daguilar43/proyectoEmbebidos/Riot/sd1306_i2c/main.c

/*
 * Copyright (C) 2016 Bas Stottelaar <basstottelaar@gmail.com>
 *
 * This file is subject to the terms and conditions of the GNU Lesser
 * General Public License v2.1. See the file LICENSE in the top level
 * directory for more details.
 */

/**
 * @ingroup     tests
 * @{
 *
 * @file
 * @brief       Test application for the U8g2 package.
 *
 * @author      Bas Stottelaar <basstottelaar@gmail.com>
 *
 * @}
 */

#ifndef INDEX_DRIVER_HW_I2C
#error "INDEX_DRIVER_HW_I2C not defined"
#endif

#ifndef TEST_ADDR
#error "TEST_ADDR not defined"
#endif

#ifndef SETUP_DISPLAY
#error "SETUP_DISPLAY not defined"
#endif

#ifndef TEST_PIN_RESET
#error "TEST_PIN_RESET not defined"
#endif

#include <stdio.h>

#include "periph/gpio.h"
#include "periph/i2c.h"

#include "timex.h"
#include "ztimer.h"

#include "u8g2.h"
#include "u8x8_riotos.h"

/**
 * @brief   RIOT-OS logo, 64x32 pixels at 8 pixels per byte.
 */
static const uint8_t logo[] = {

// 'amiplanta128x64', 128x64px
0xff, 0xff, 0xff, 0xff, 0xff, 0xff, 0xff, 0xff, 0xff, 0xff, 0xff, 0xff, 0xff, 0xff, 0xff, 0xff, 
0xff, 0xff, 0xff, 0xff, 0xff, 0xff, 0xff, 0xf8, 0x1f, 0xff, 0xff, 0xff, 0xff, 0xff, 0xff, 0xff, 
0xff, 0xff, 0xff, 0xff, 0xff, 0xff, 0xff, 0xe0, 0x07, 0xff, 0xff, 0xff, 0xff, 0xff, 0xff, 0xff, 
0xff, 0xff, 0xff, 0xff, 0xff, 0xff, 0xff, 0xc3, 0xe1, 0xff, 0xff, 0xff, 0xff, 0xff, 0xff, 0xff, 
0xff, 0xff, 0xff, 0xff, 0xff, 0xff, 0xff, 0x0f, 0xf0, 0xff, 0xff, 0xff, 0xff, 0xff, 0xff, 0xff, 
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

    u8g2_InitDisplay(&u8g2);
    u8g2_SetPowerSave(&u8g2, 0);

    /* start drawing in a loop */
    puts("Drawing on screen.");

    while (1) {
        u8g2_FirstPage(&u8g2);

        do {
            u8g2_SetDrawColor(&u8g2, 1);
            u8g2_SetFont(&u8g2, u8g2_font_helvB12_tf);

            switch (screen) {
                case 0:
                    u8g2_DrawStr(&u8g2, 12, 22, "THIS");
                    break;
                case 1:
                    u8g2_DrawStr(&u8g2, 24, 22, "IS");
                    break;
                case 2:
                    u8g2_DrawBitmap(&u8g2, 0, 0, 16, 53, logo);
                    u8g2_DrawStr(&u8g2, 24, 65, "AMIPLANTA!");
                    break;
            }
        } while (u8g2_NextPage(&u8g2));

        /* show screen in next iteration */
        screen = (screen + 1) % 3;

        /* sleep a little */
        ztimer_sleep(ZTIMER_USEC, US_PER_SEC);
    }

    return 0;
}
