daguilar43/proyectoEmbebidos/CodigoFinal/sd1306_i2c/perifericos/carasPantalla.c

#ifndef INDEX_DRIVER_HW_I2C
#error "INDEX_DRIVER_HW_I2C not defined"
#endif

#ifndef TEST_ADDR
#error "TEST_ADDR not defined"
#endif

#ifndef SETUP_DISPLAY
#error "SETUP_DISPLAY not defined"
#endif

#ifndef TEST_PIN_RESET
#error "TEST_PIN_RESET not defined"
#endif

#include <stdio.h>

#include "periph/gpio.h"
#include "periph/i2c.h"

#include "timex.h"
#include "ztimer.h"

#include "u8g2.h"
#include "u8x8_riotos.h"
#include "periph/adc.h"
#include "sensorLuz.c"

#include "adc.c"
#define FPS 5  /// Cantidad de Fotogramas en la pantalla por segundo



#define umbralTemp   15       // Zona estable de temperatura    
#define umbralLuz    10       /// Solo se considera luz muy baja 
#define umbralHumedad 10 
#define umbralSuperiorHumendad 50  

#define humedadIdeal 40  ///// Despues de conversion a porcentaje  


int tempIdeal=25;   // Despues de caracterizacion de valores de grados centigrados
int luzIdeal=24;   ///// Despues de caracterizacion de valores (adc)

//const int gpioTempInit =10;
/// Prioridad :   Controlabilidad   1.Humedad 2.Luz 3.temperatura

u8g2_t u8g2;


u8x8_riotos_t user_data =
    {
        .device_index = INDEX_DRIVER_HW_I2C,
        .pin_cs = TEST_PIN_CS,
        .pin_dc = TEST_PIN_DC,
        .pin_reset = TEST_PIN_RESET,
    };

/**
 * @brief   RIOT-OS logo, 64x32 pixels at 8 pixels per byte.
 */
static const uint8_t logoRiot[] = {
    0x00, 0x00, 0x00, 0x00, 0x00, 0x00, 0x00, 0x00, 0x00, 0x00, 0x03, 0xE0,
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
	0xff, 0xff, 0xff, 0xff, 0xff, 0xff, 0xc3, 0xff, 0xff, 0xc3, 0xff, 0xff, 0xff, 0xff, 0xff, 0xff,				
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
};			

static const uint8_t  *animacionFeliz[]={caraFeliz1,caraFeliz2,caraFeliz3,caraFeliz2};
static const int lengthAnimacionFeliz=4;
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
